sapir/eink-adapter/src/wemos_d1_mini.h

#ifndef __WEMOS_D1_MINI_H__
#define __WEMOS_D1_MINI_H__


#define PIN_D0  16
#define PIN_D1  5
#define PIN_D2  4
#define PIN_D3  0
#define PIN_D4  2
#define PIN_D5  14
#define PIN_D6  12
#define PIN_D7  13
#define PIN_D8  15
#define PIN_TX  1
#define PIN_RX  3

#define PIN_LED PIN_D2


#endif
